whatthefilament/Framework-AIO/Images/Assembly Instruction Manual Pictures/IMG_1828 (1).jpeg

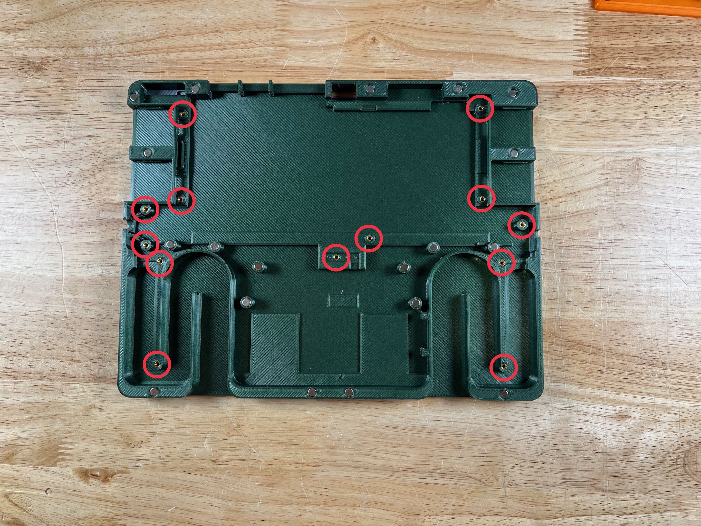
Images/Assembly Instruction Manual Pictures/IMG_1828 (1).jpeg
