whatthefilament/Framework-AIO/Images/Assembly Instruction Manual Pictures/IMG_1830.jpeg

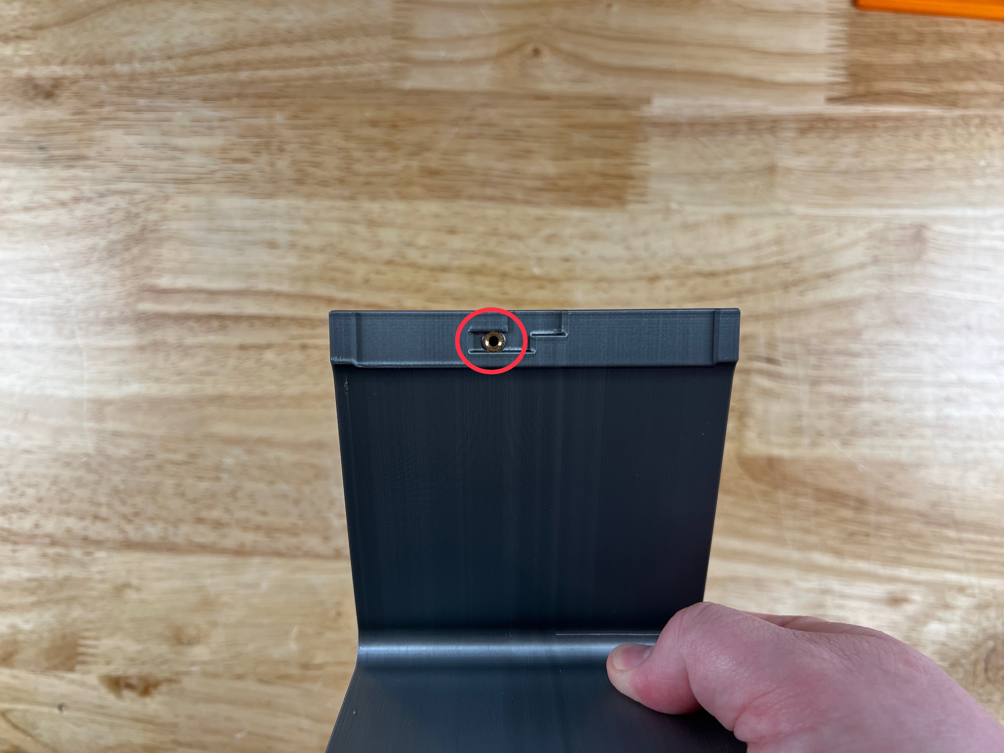
Images/Assembly Instruction Manual Pictures/IMG_1830.jpeg
