whatthefilament/Framework-AIO/Images/Assembly Instruction Manual Pictures/IMG_1831.jpeg

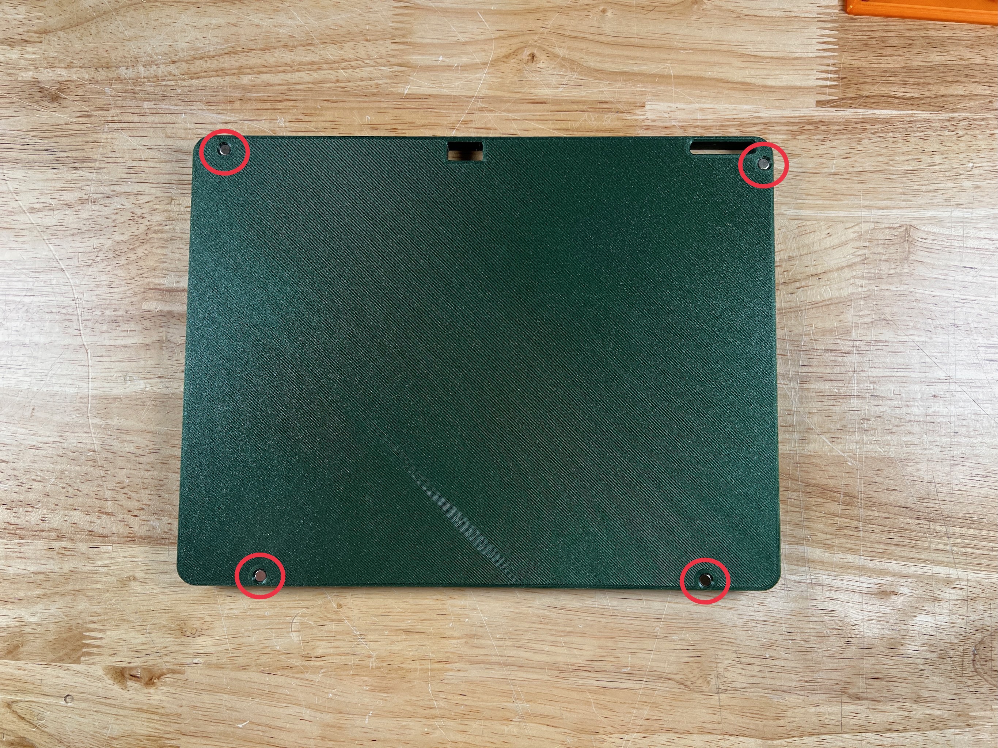
Images/Assembly Instruction Manual Pictures/IMG_1831.jpeg
