whatthefilament/Framework-AIO/Images/Assembly Instruction Manual Pictures/IMG_1832.jpeg

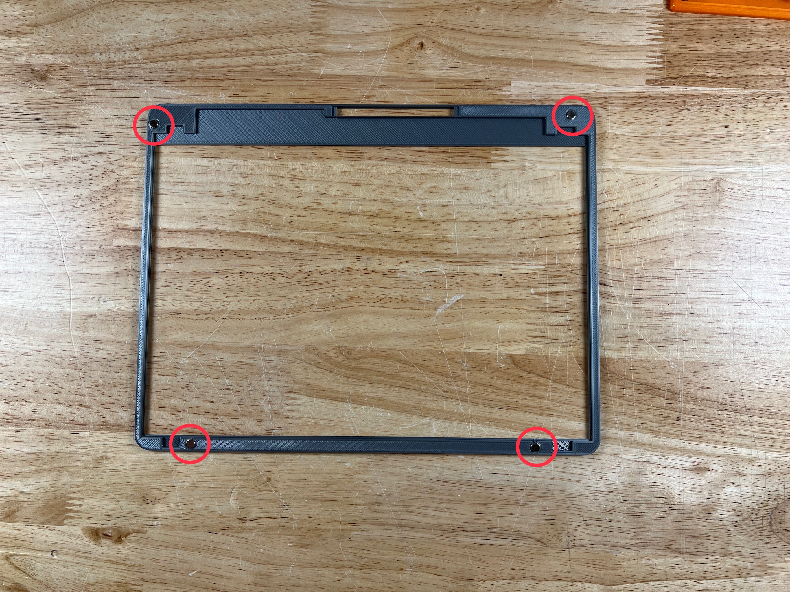
Images/Assembly Instruction Manual Pictures/IMG_1832.jpeg
