whatthefilament/Framework-AIO/Images/Assembly Instruction Manual Pictures/IMG_1833.jpeg

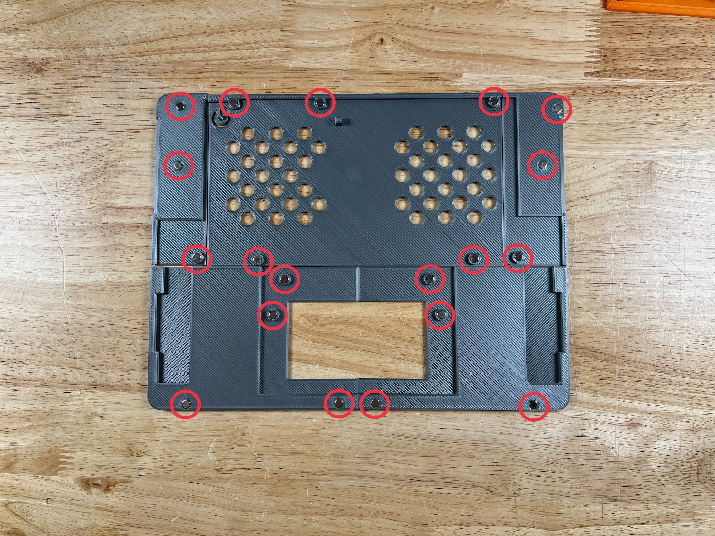
Images/Assembly Instruction Manual Pictures/IMG_1833.jpeg
