whatthefilament/Framework-AIO/Images/Assembly Instruction Manual Pictures/IMG_1834.jpeg

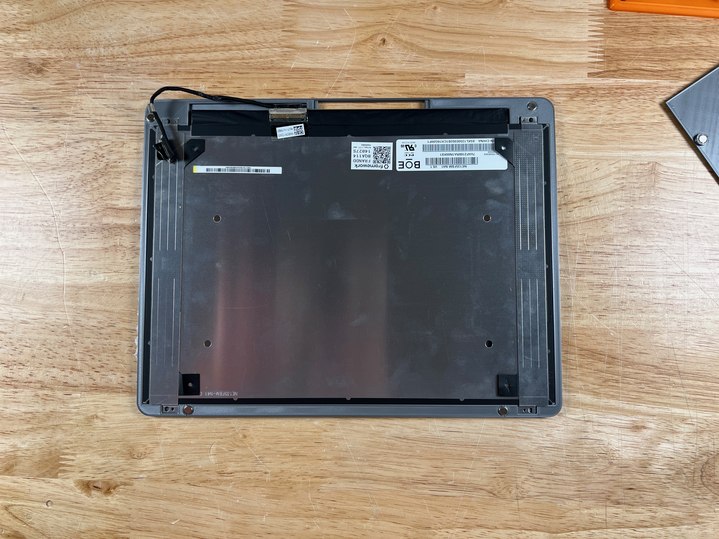
Images/Assembly Instruction Manual Pictures/IMG_1834.jpeg
