whatthefilament/Framework-AIO/Images/Assembly Instruction Manual Pictures/IMG_1836.jpeg

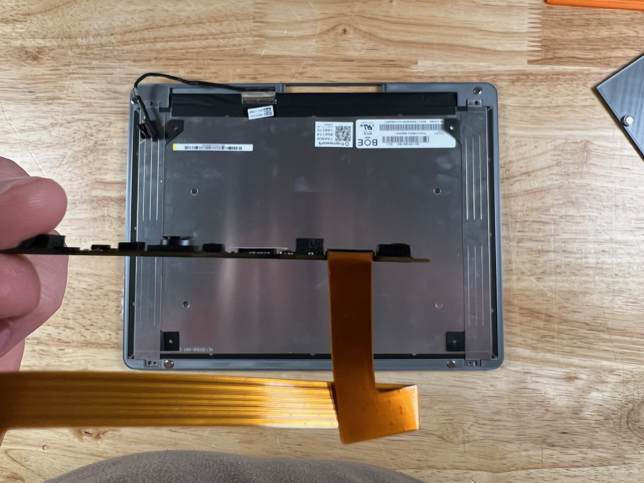
Images/Assembly Instruction Manual Pictures/IMG_1836.jpeg
