whatthefilament/Framework-AIO/Images/Assembly Instruction Manual Pictures/IMG_1837.jpeg

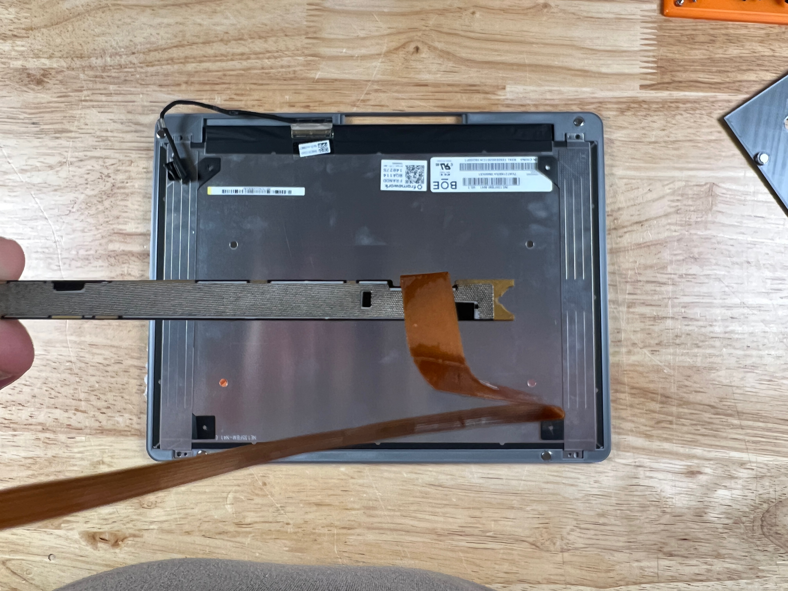
Images/Assembly Instruction Manual Pictures/IMG_1837.jpeg
