whatthefilament/Framework-AIO/Images/Assembly Instruction Manual Pictures/IMG_1838.jpeg

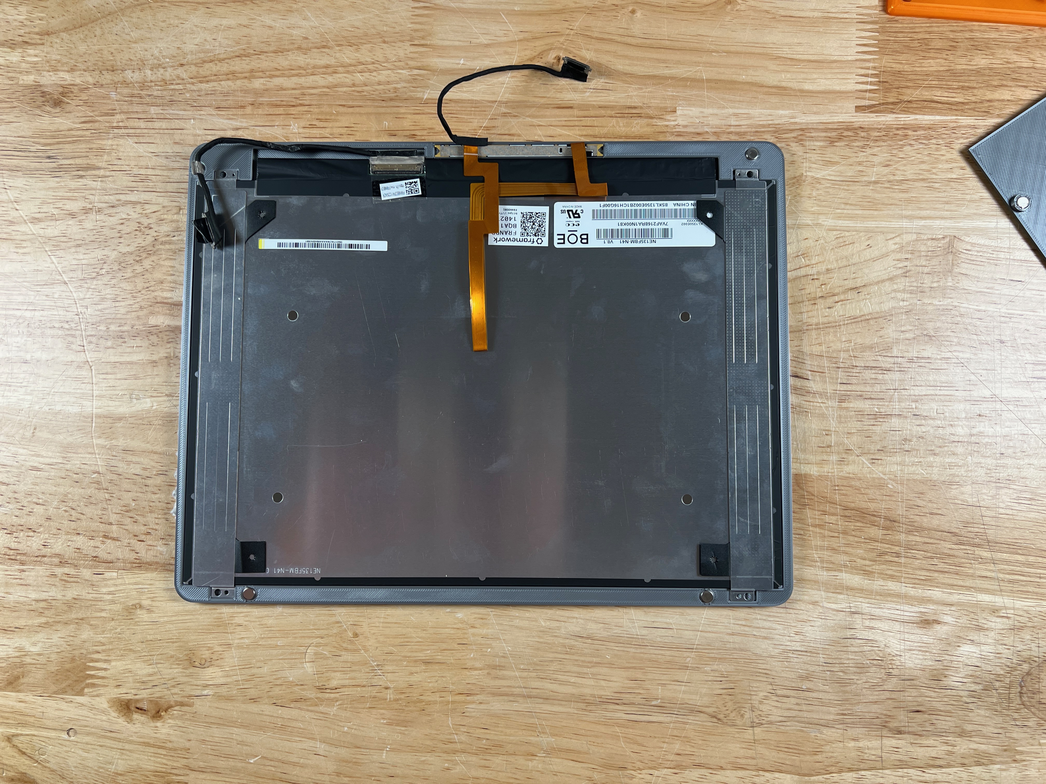
Images/Assembly Instruction Manual Pictures/IMG_1838.jpeg
