whatthefilament/Framework-AIO/Images/Assembly Instruction Manual Pictures/IMG_1841.jpeg

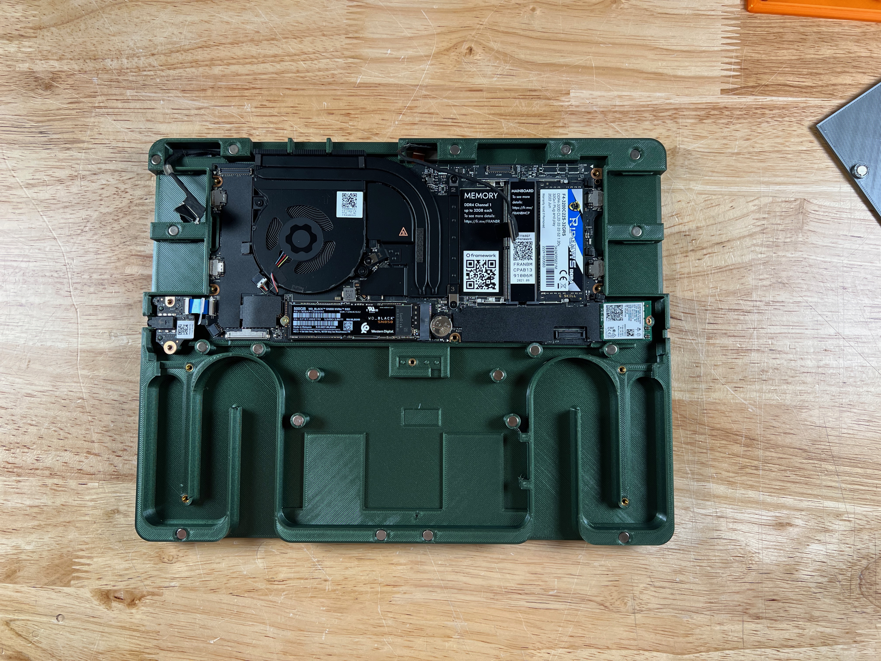
Images/Assembly Instruction Manual Pictures/IMG_1841.jpeg
