whatthefilament/Framework-AIO/Images/Assembly Instruction Manual Pictures/IMG_1844.jpeg

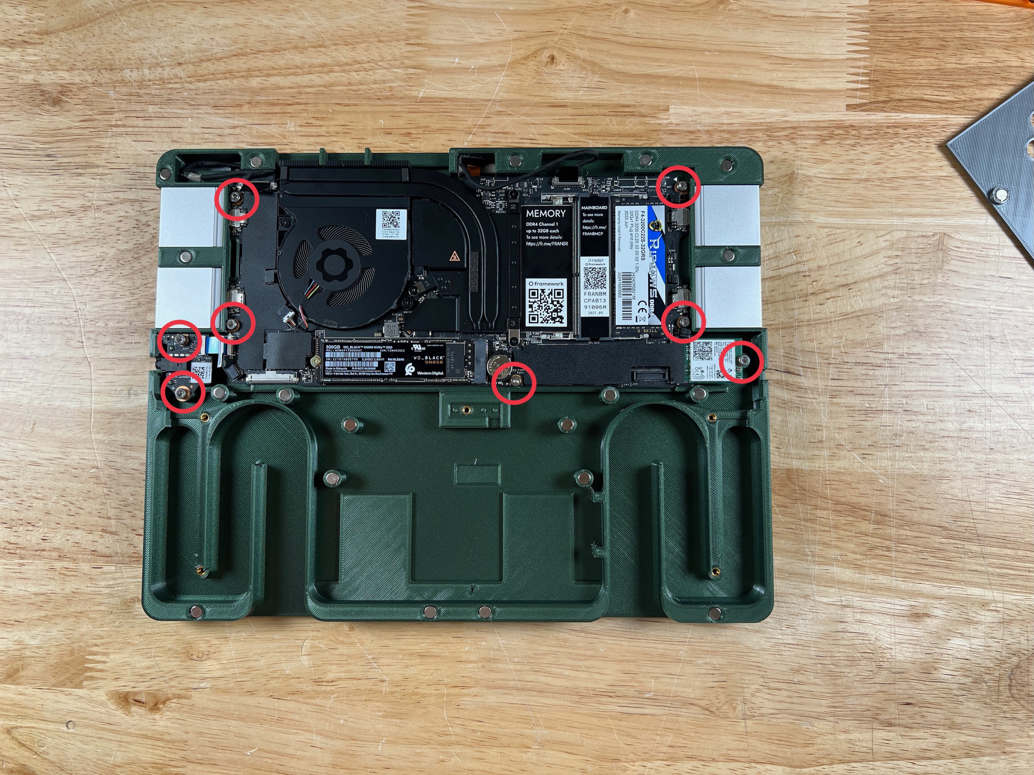
Images/Assembly Instruction Manual Pictures/IMG_1844.jpeg
