whatthefilament/Framework-AIO/Images/Assembly Instruction Manual Pictures/IMG_1846.jpeg

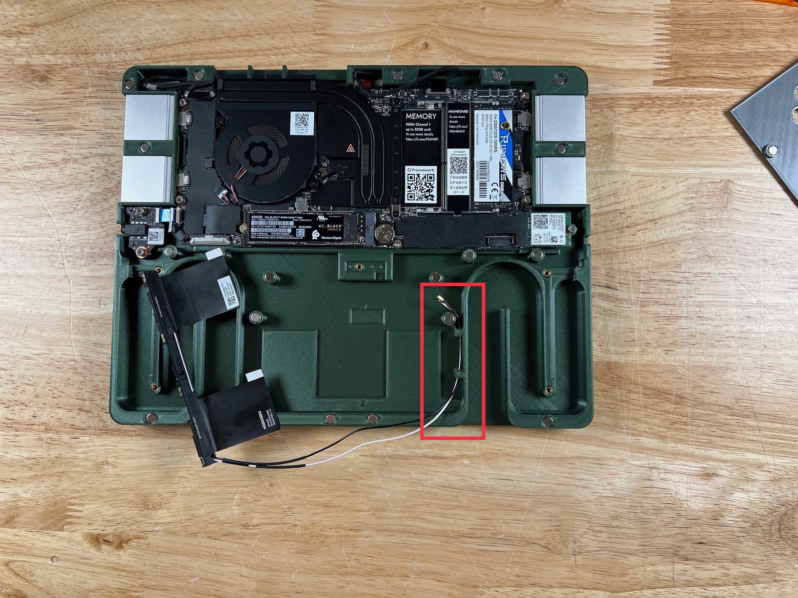
Images/Assembly Instruction Manual Pictures/IMG_1846.jpeg
