whatthefilament/Framework-AIO/Images/Assembly Instruction Manual Pictures/IMG_1847.jpeg

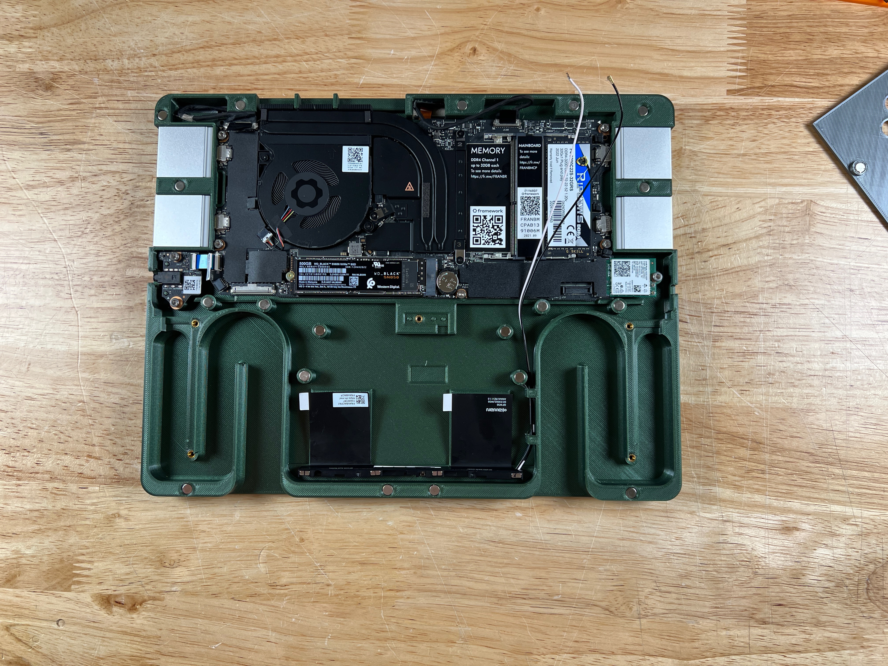
Images/Assembly Instruction Manual Pictures/IMG_1847.jpeg
