whatthefilament/Framework-AIO/Images/Assembly Instruction Manual Pictures/IMG_1848.jpeg

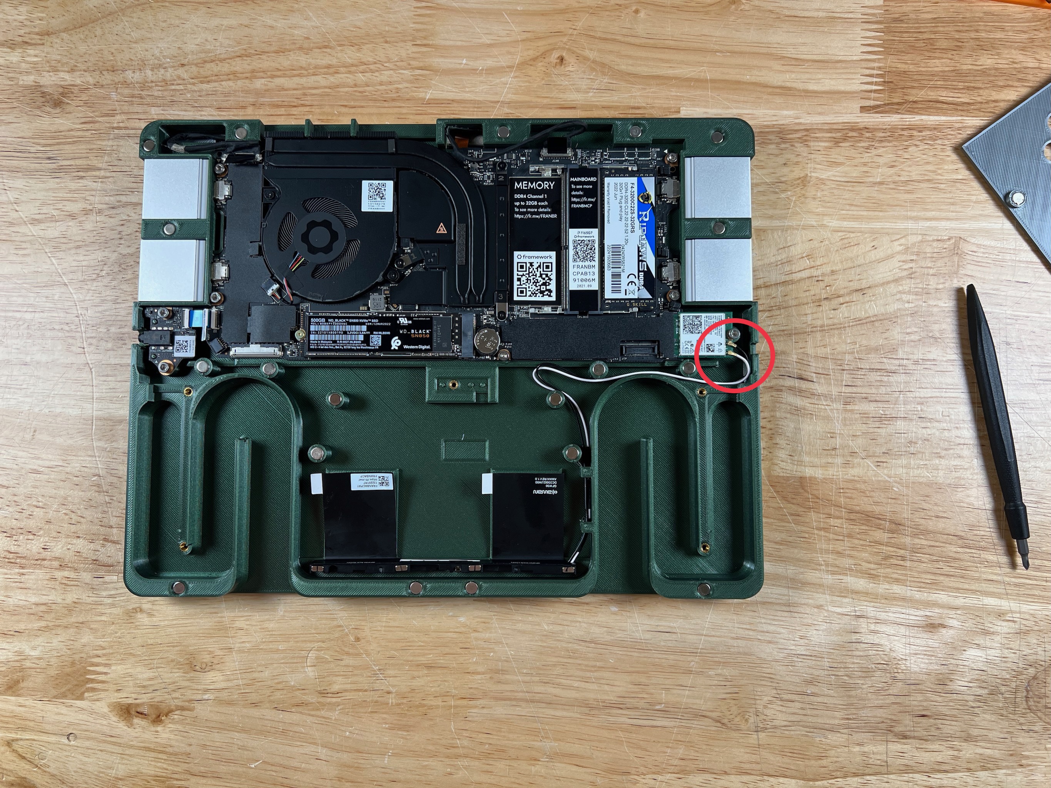
Images/Assembly Instruction Manual Pictures/IMG_1848.jpeg
