whatthefilament/Framework-AIO/Images/Assembly Instruction Manual Pictures/IMG_1849.jpeg

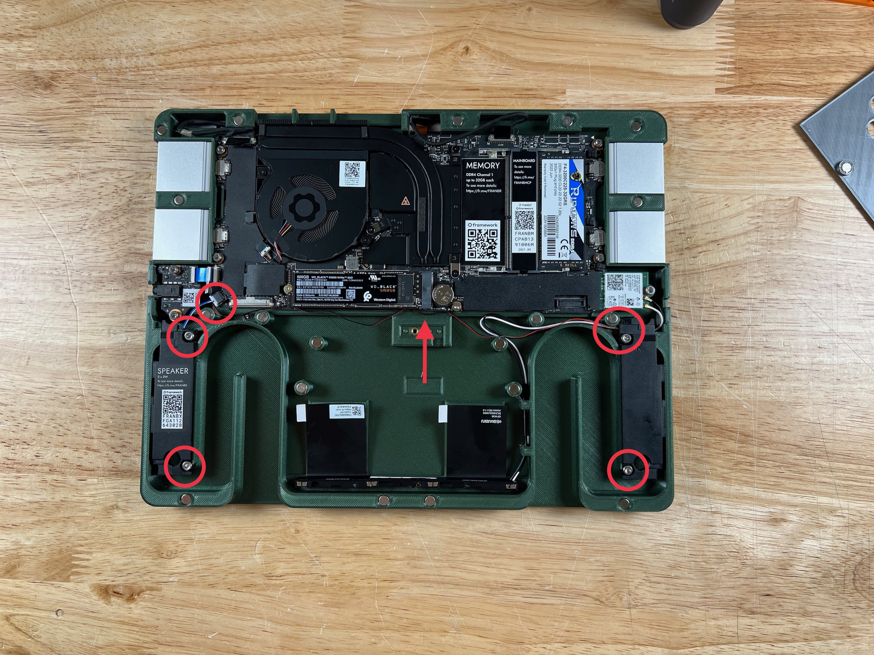
Images/Assembly Instruction Manual Pictures/IMG_1849.jpeg
