whatthefilament/Framework-AIO/Images/Assembly Instruction Manual Pictures/IMG_1850.jpeg

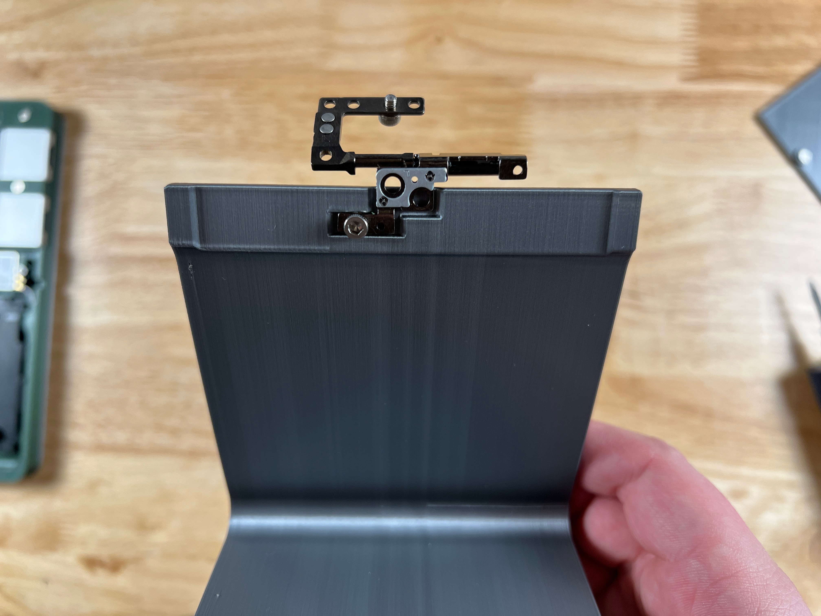
Images/Assembly Instruction Manual Pictures/IMG_1850.jpeg
