whatthefilament/Framework-AIO/Images/Assembly Instruction Manual Pictures/IMG_1854.jpeg

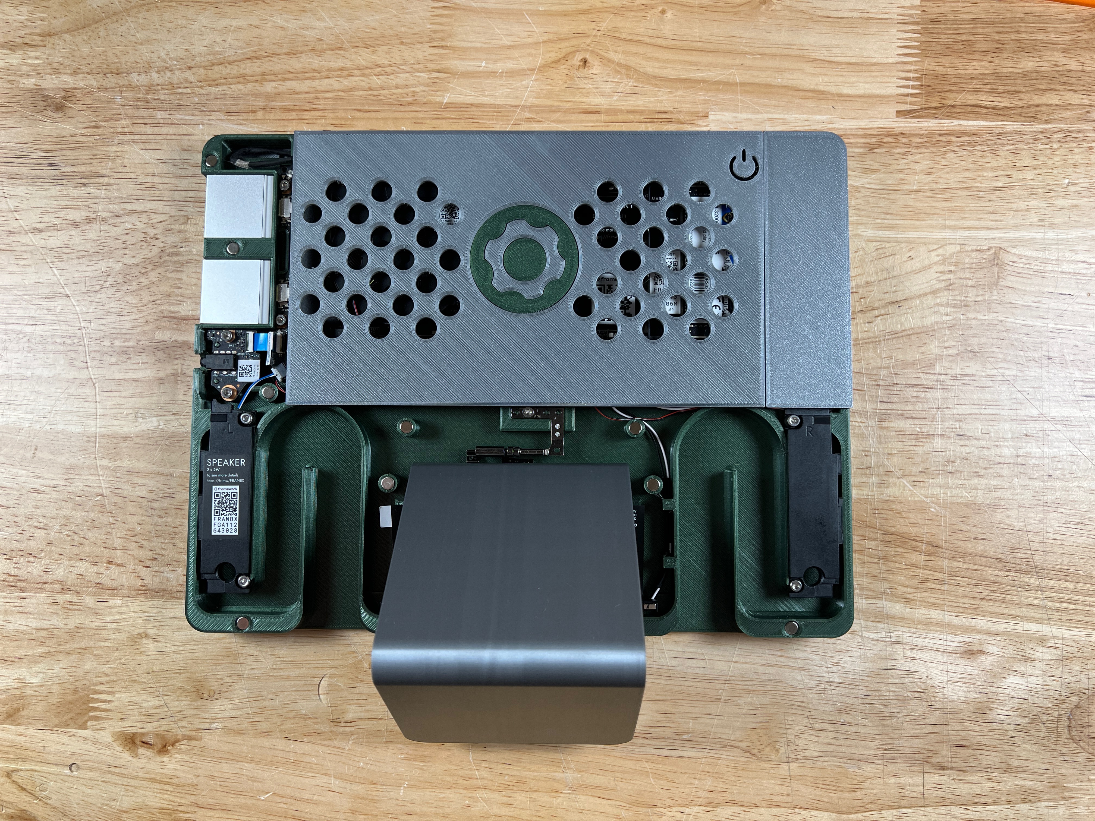
Images/Assembly Instruction Manual Pictures/IMG_1854.jpeg
