whatthefilament/Framework-AIO/Images/Assembly Instruction Manual Pictures/IMG_1861.jpeg

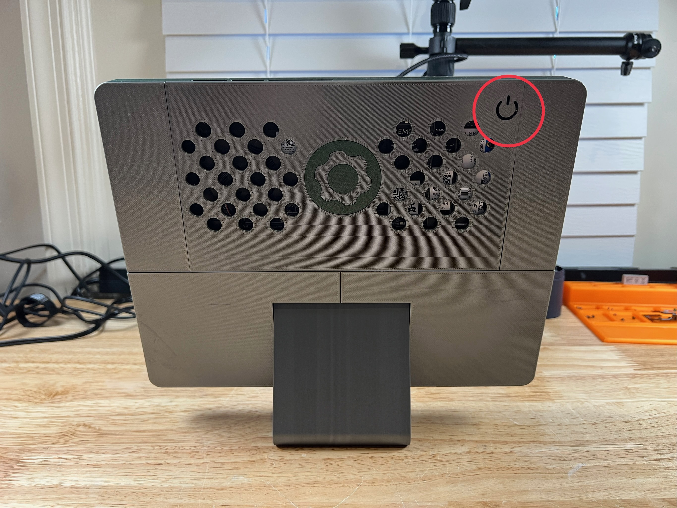
Images/Assembly Instruction Manual Pictures/IMG_1861.jpeg
