whatthefilament/Framework-AIO/Images/Assembly Instruction Manual Pictures/IMG_1864.jpeg

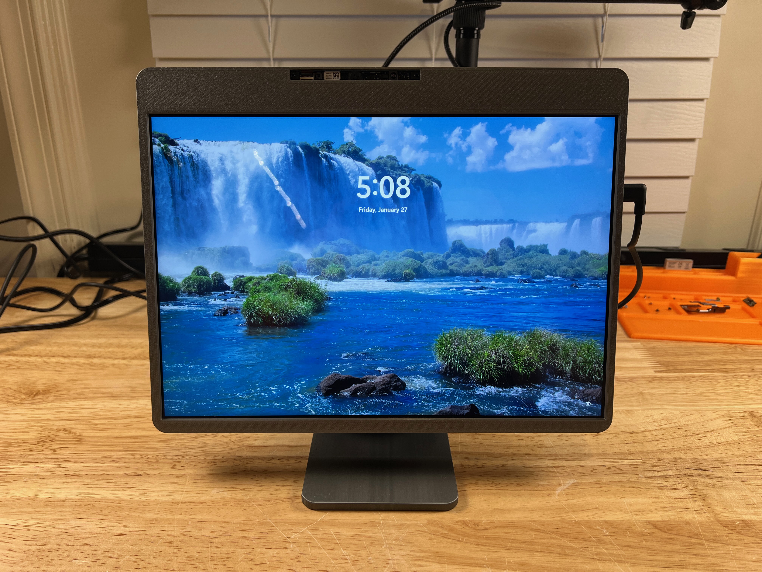
Images/Assembly Instruction Manual Pictures/IMG_1864.jpeg
